txp666/ChaZuo/esp8266程序/库文件/5.HomeKit/my_accessory.c

/*
 * my_accessory.c
 * Define the accessory in C language using the Macro in characteristics.h
 *
 *  Created on: 2020-05-15
 *      Author: Mixiaoxiao (Wang Bin)
 */

#include <homekit/homekit.h>
#include <homekit/characteristics.h>

void my_accessory_identify(homekit_value_t _value) {
    printf("accessory identify\n");
}

// Switch (HAP section 8.38)
// required: ON
// optional: NAME

// format: bool; HAP section 9.70; write the .setter function to get the switch-event sent from iOS Home APP.
homekit_characteristic_t cha_switch_on = HOMEKIT_CHARACTERISTIC_(ON, false);

// format: string; HAP section 9.62; max length 64
homekit_characteristic_t cha_name = HOMEKIT_CHARACTERISTIC_(NAME, "Switch");

homekit_accessory_t* accessories[] = {
    HOMEKIT_ACCESSORY(.id = 1, .category = homekit_accessory_category_switch, .services = (homekit_service_t * []) {
        HOMEKIT_SERVICE(ACCESSORY_INFORMATION, .characteristics = (homekit_characteristic_t * []) {
            HOMEKIT_CHARACTERISTIC(NAME, "202104134"),
            HOMEKIT_CHARACTERISTIC(MANUFACTURER, "Arduino HomeKit"),
            HOMEKIT_CHARACTERISTIC(SERIAL_NUMBER, "123456"),
            HOMEKIT_CHARACTERISTIC(MODEL, "ESP8266/ESP32"),
            HOMEKIT_CHARACTERISTIC(FIRMWARE_REVISION, "1.0"),
            HOMEKIT_CHARACTERISTIC(IDENTIFY, my_accessory_identify),
            NULL
        }),
        HOMEKIT_SERVICE(SWITCH, .primary = true, .characteristics = (homekit_characteristic_t * []){
            &cha_switch_on,
            &cha_name,
            NULL
        }),
        NULL
    }),
    NULL
};

homekit_server_config_t config = {
        .accessories = accessories,
        .password = "666-66-666"
};
