txp666/ChaZuo/esp8266程序/库文件/5.HomeKit/wifi_info.h

/*
 * wifi_info.h
 *
 *  Created on: 2020-05-15
 *      Author: Mixiaoxiao (Wang Bin)
 */

#ifndef WIFI_INFO_H_
#define WIFI_INFO_H_

#if defined(ESP8266)
#include <ESP8266WiFi.h>
#elif defined(ESP32)
#include <WiFi.h>
#endif

const char *ssid = "666";//填写自己的WIFI名
const char *password = "12345678";//WIFI密码

void wifi_connect() {
	WiFi.persistent(false);
	WiFi.mode(WIFI_STA);
	WiFi.setAutoReconnect(true);
	WiFi.begin(ssid, password);
	Serial.println("WiFi connecting...");
	while (!WiFi.isConnected()) {
		delay(100);
		Serial.print(".");
	}
	Serial.print("\n");
	Serial.printf("WiFi connected, IP: %s\n", WiFi.localIP().toString().c_str());
}

#endif /* WIFI_INFO_H_ */
